SuperHouse/EtherUno/Images/ETHERUNO-teaser.jpeg

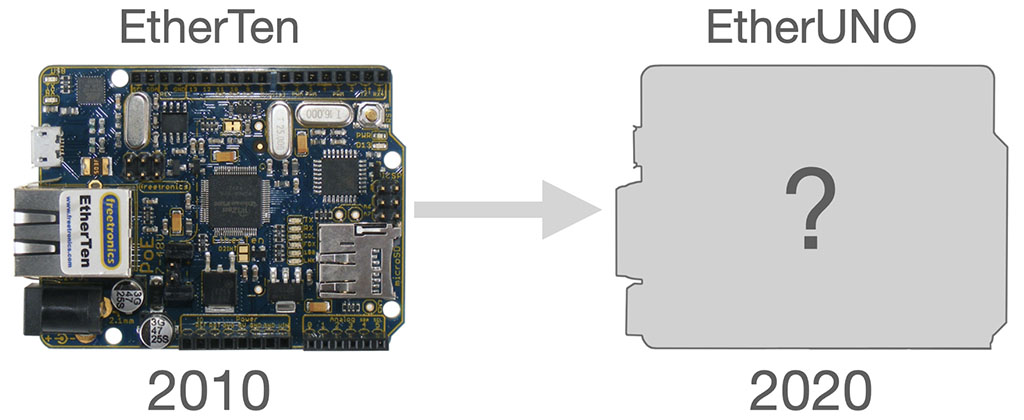
Images/ETHERUNO-teaser.jpeg
